lunacrest01/core-macropad/production/firmware/config.h

#ifndef CONFIG_H
#define CONFIG_H

// Matrix pins
#define ROW1    1
#define ROW2    2
#define ROW3    3
#define COL1    7
#define COL2    8
#define COL3    9


#define ENC_A   10
#define ENC_B   12


#define RGB_DATA_PIN 4
#define NUM_LEDS     1


#define BATTERY_PIN     34      
#define CHARGING_PIN    14    

#define DEVICE_NAME        "core"
#define MANUFACTURER_NAME  "lunacrest"

#endif
