lunacrest01/core-macropad/production/firmware/keymap.cpp

#include "keymap.h"

const uint8_t keymaps[LAYERS][ROWS][COLS] = {
    { 
        {0x04, 0x05, 0x06},  
        {0x07, 0x08, 0x09},  
        {0x0A, 0x0B, 0x0C}   
    },
    { 
        {0x1E, 0x1F, 0x20},  
        {0x21, 0x22, 0x23}, 
        {0x24, 0x25, 0x26}  
    },
    { 
        {0xE2, 0xEA, 0xE9}, 
        {0x00, 0x00, 0x00},  
        {0x00, 0x00, 0x00}
    }
};


const EncoderAction encoder_actions[LAYERS] = {
    {0x4F, 0x50},       
    {0x51, 0x52},          
    {0xE9, 0xEA}          
};
